pramodsandaruwan/walkie_messenger/media/img01.jpg

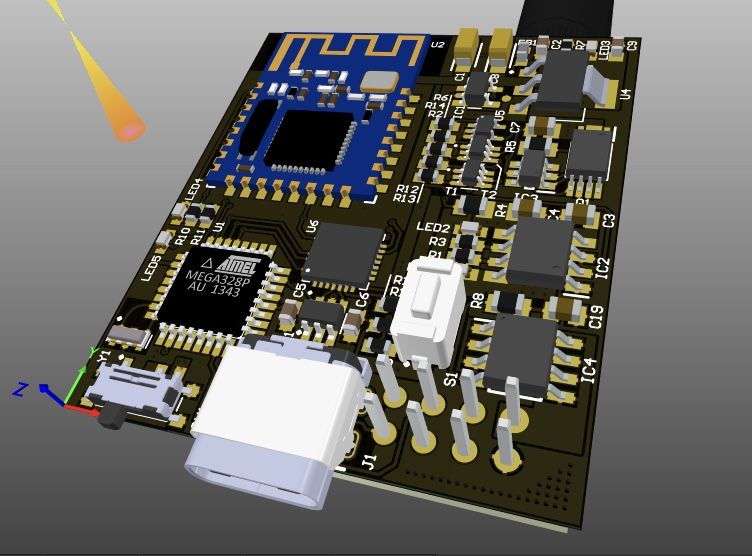
media/img01.jpg
