pramodsandaruwan/walkie_messenger/media/img03.JPG

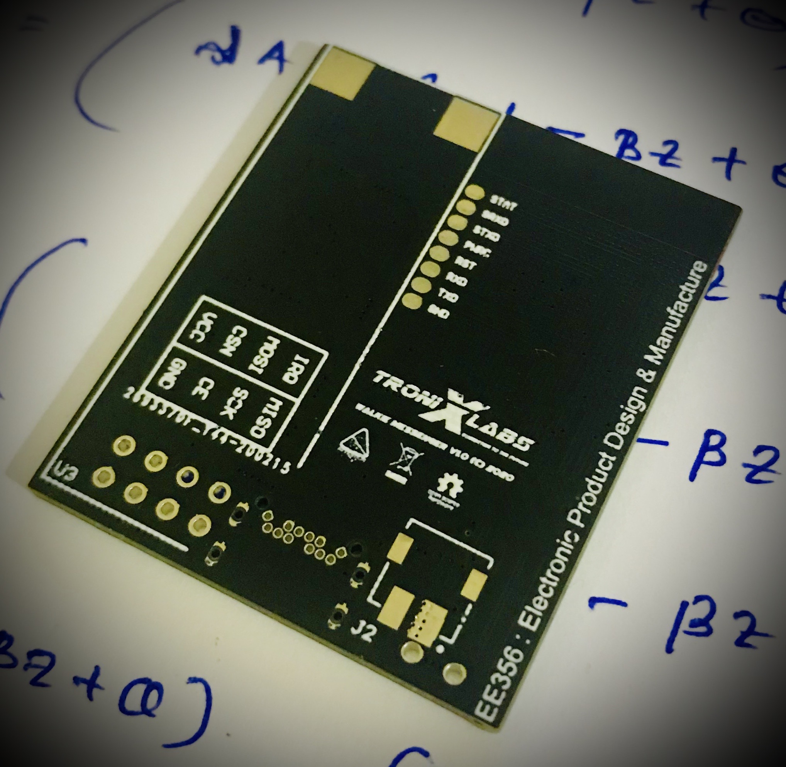
media/img03.JPG
