pramodsandaruwan/walkie_messenger/media/img04.JPG

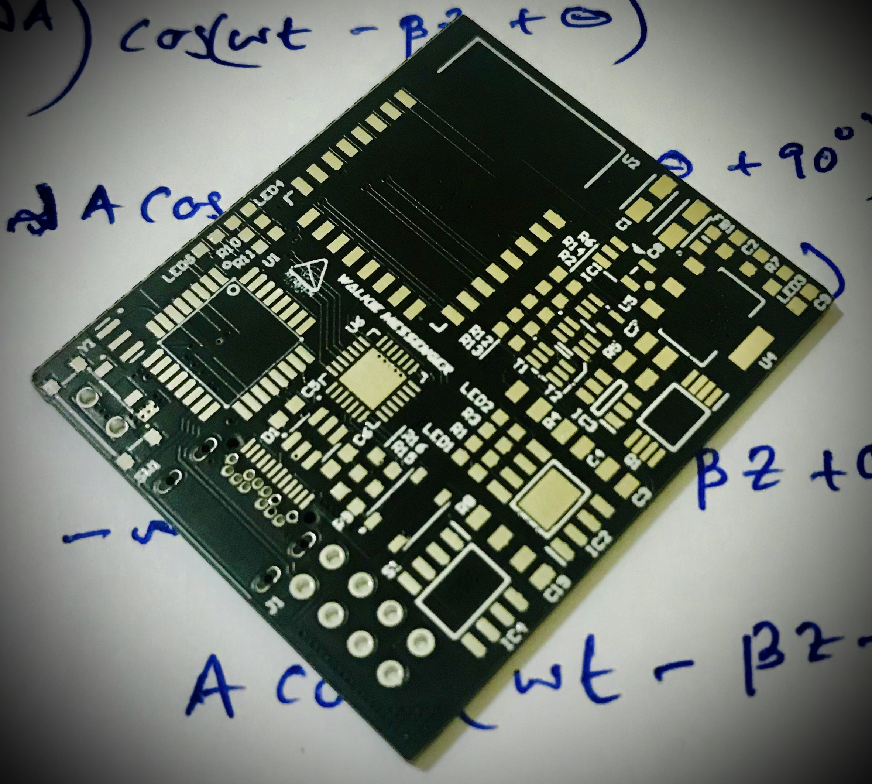
media/img04.JPG
